millillitre/Smart_Devices/docs/Mask.jpg

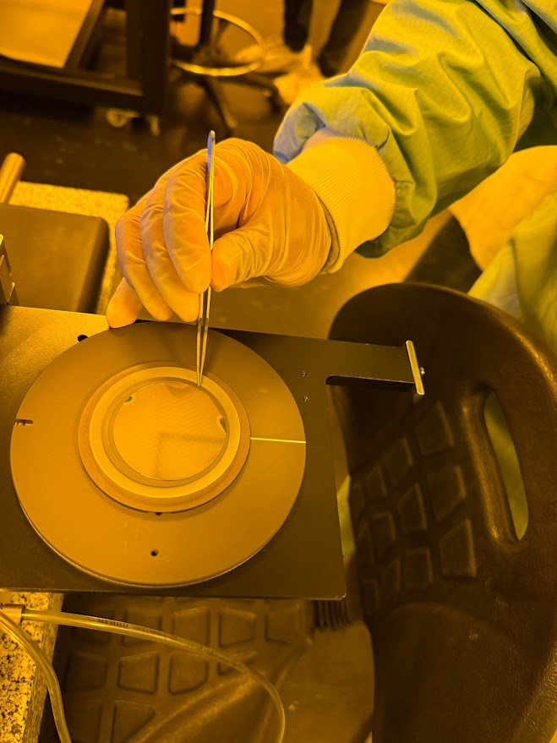
docs/Mask.jpg
