millillitre/Smart_Devices/MIT_App/Application/block_screen1.png

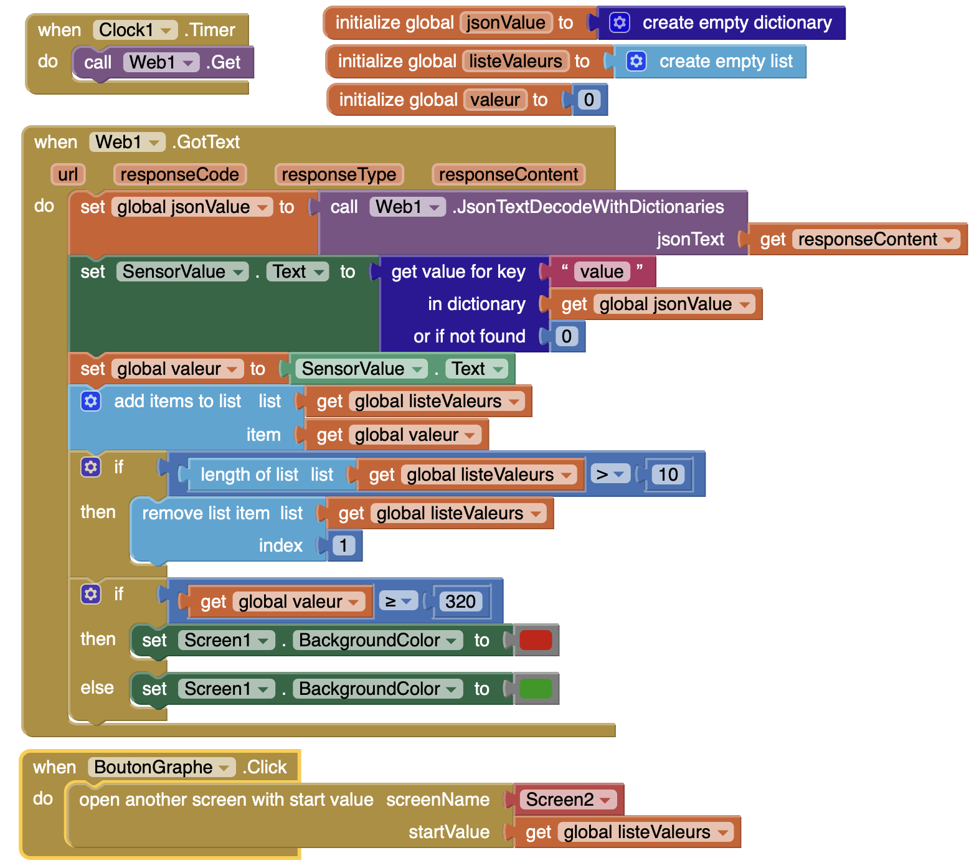
MIT_App/Application/block_screen1.png
