millillitre/Smart_Devices/MIT_App/Application/block_screen2.png

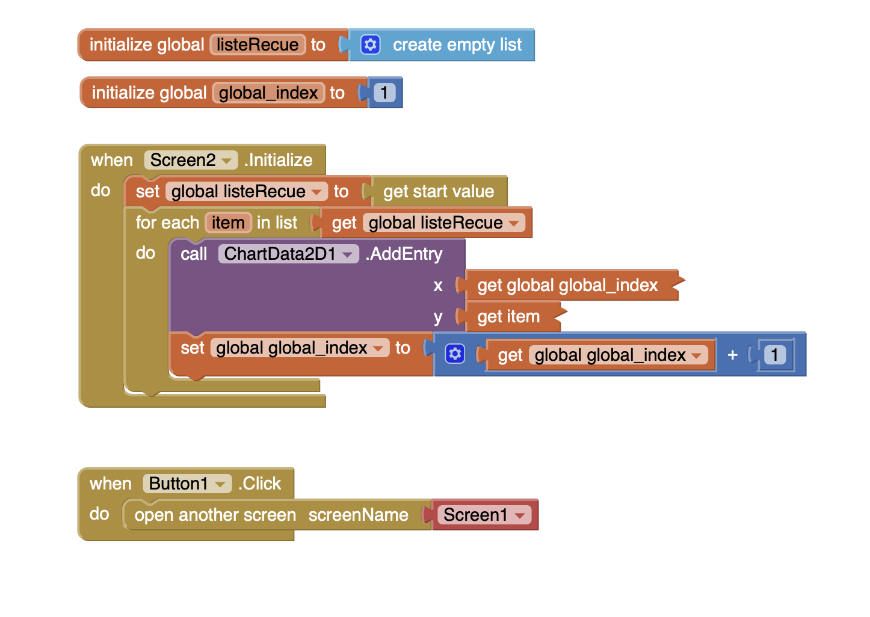
MIT_App/Application/block_screen2.png
