millillitre/Smart_Devices/NodeRED/flows2.png

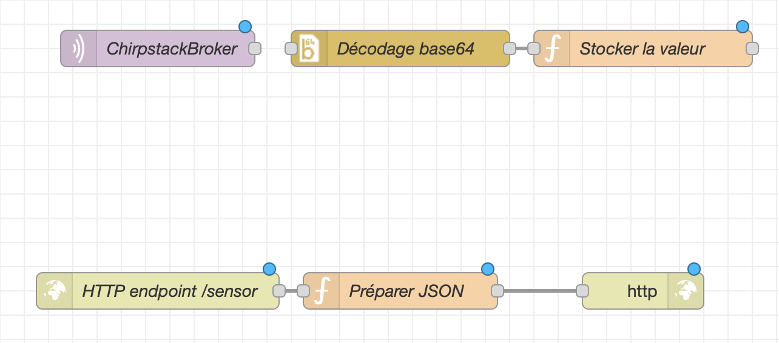
NodeRED/flows2.png
