millillitre/Smart_Devices/LTSpice/ampliyoplait_avec_capteur.asc

C5: cap; 100n
C6: cap; 100n
C7: cap; 100n
C8: cap; 1µ
I2: current; PULSE(50n 100n 1 0.1 0.1 2); AC 1 0
R4: res; 100k
R7: res; 1k
R8: res; 100k
R9: res; 10k
R10: res; 1k
U2: LTC1050
V1: voltage; PULSE(0 1 0.2 0.1 0.1 20)
V2: voltage; 5
X1: le_gros_capteur
Named nets: 0, ADC, Isens
.tran 5
;ac dec 100 1 1g
