millillitre/Smart_Devices/LTSpice/le_gros_capteur.asc

B1: bi; I=V(cp,cn)*(10n+v(cp,cn)*10n)
C1: cap; 200µ
R1: res; 1k
Named nets: gc, gp, gn, cp, cn
